grodansparadis/can4vscp_sanfrancisco_barometer/docs/BMP180 Barometric Pressure Sensor Hookup - learn.sparkfun.com_files/52cf0a67ce395f924c8b4569.jpg

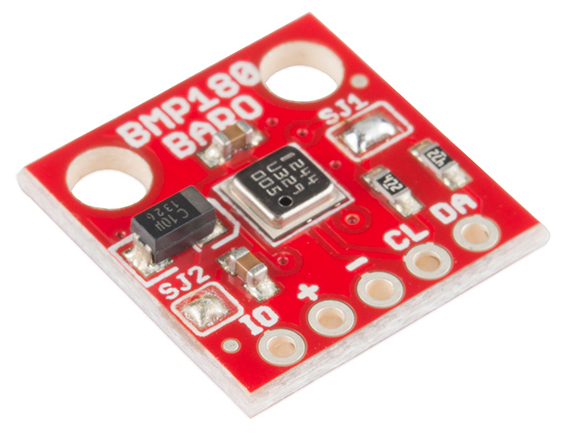
docs/BMP180 Barometric Pressure Sensor Hookup - learn.sparkfun.com_files/52cf0a67ce395f924c8b4569.jpg
