grodansparadis/can4vscp_sanfrancisco_barometer/docs/Oru-Te-EXE084-EL108-04.pdf

Örebro universitet | Örebro University
Institutionen för teknik | Department of technology
701 82 Örebro | SE-701 82 Örebro, Sweden

## Examensarbete 10 po‰ng C-nivÂ

# KONSTRUKTION OCH TILLVERKNING AV

# DENSITETSMƒTARE

## Johan Landmark och Oscar Tryggvesson

## Elektronikingenjˆrsprogrammet 120 po‰ng

## ÷rebro vÂrterminen 2004

Examinator: Sune Bergelin
Handledare: Thorbjˆrn Andersson

Luftdensitetsm‰tare | 2005-05-22

## Fˆrord

Vi vill tacka fˆljande personer. Kjell MÂrdensjˆ fˆr din hj‰lp med programmering av AVR-processorn, Torbjˆrn Andersson (Telnek) fˆr ditt aktiva stˆd genom hela projektet, Thomas
M. Poms fˆr dina idÈer kring konstruktionen av vÂr prototyp, fˆr ert stˆd i vÂrt projektarbete.

÷rebro 2002-12-11

__________________ | __________________
Johan Landmark | Oscar Tryggvesson

## Sammanfattning

Examensarbetet bestÂr av att konstruera en prototyp fˆr m‰tning av luftdensitet i f‰lt. Prototypen ‰mnar underl‰tta inst‰llningarna av fˆrgasare dÂ den ger m‰tv‰rden kontinuerligt pÂ plats. Fˆrhoppningsvis kommer den att spara tid till anv‰ndaren dÂ han/hon inte behˆver sˆka efter v‰rden fˆr att sedan r‰kna ut luftens densitet.

Hj‰rnan i prototypen bestÂr av en AvR mikroprocessor som utfˆr ber‰kningar och visar resultatet pÂ en LCD-display. Densiteten ber‰knas utgÂende frÂn luftfuktighet, lufttryck och temperatur vilket fÂs frÂn givare inbyggda i konstruktionen.

Kraven fˆr examensarbetet ‰r att bygga en prototyp som klarar av att m‰ta luftens densitet i temperatur omrÂdet -10ºC till +50ºC. Fˆr en mer detaljerad beskrivning se kravspecifikationen sid. 9.

MÂlet med vÂrt projekt ‰r att konstruera prototypen inom 10 veckor samt att uppfylla vÂra krav.

Resultatet av projektet med h‰nsyn taget till fˆruts‰ttningar, anser vi blivit bra. Produkten blev aldrig helt f‰rdigkonstruerad och noggrannheten i m‰tningen blev inte heller vad vi hade t‰nkt oss. Trots detta har vi l‰rt oss mycket inom detta nya omrÂde.

## Abstract

Our thesis consists in developing a prototype for field measurement that measures air density. The prototype is meant to relieve the job when calibrating fuel injectors when it provides measurement values continuously. Hopefully it will save time for the user thus he/she doesnít need to look for air density values.

The brain in our construction is the AvR microprocessor that performs calculations and presents the result on an LCD-display. The air density is calculated by values given from the sensors.

The objektive was to build a prototype that manages to calculate the air density between -10°C to +50°C. For more detailed specification se page 9.

Our target was to construct the prototyp within 10 weeks and to satesfy our demands.

The project result considering the limited resources in terms of material, we think that the thesis has worked out well. The product never got finished and the accuracy didnít get as good as we hoped. However we learned a lot in this new area.

## InnehÂllsfˆrteckning

## Bilder

## 1 Introduktion

### 1.1 Bakgrund

Vid karting, gokartt‰vlingar, trimmas motorernas olika delar fˆr att uppnÂ optimal prestanda. En av de viktiga aspekterna ‰r fˆrgasarna eftersom det ‰r de som fˆrser motorn med br‰nsle. N‰r man justerar fˆrgasarna har luftfuktigheten en viss betydelse pÂ hur man st‰ller in dem. DÂ fˆretaget Telnik fÂtt i uppgift att tillverka en smart lˆsning till att m‰ta luftens densitet sÂ att man pÂ plats direkt kan justera fˆrgasarinst‰llningarna har vi Âtagit oss att lˆsa uppgiften som ett examensarbete och tillverka en mobil prototyp fˆr test i f‰lt.

Den stora fˆrdelen med att kunna m‰ta luftens densitet mobilt ‰r att man inte behˆver ta h‰nsyn till var i v‰rlden man t‰vlar dÂ m‰tningen och inst‰llningarna kan gˆras pÂ plats.
En lˆsning till problemet skulle spara tid och pengar, vilket ‰r tvÂ viktiga aspekter.

### 1.2 Projekt beskrivning

Projektets slutgiltiga mÂl ‰r att kunna m‰ta luftens densitet kontinuerligt.Fˆr att Âstadkomma detta kr‰vs fˆljande parametrar:
! Luftfuktighet

! Lufttryck

! Temperatur

PÂ uppdrag av Telnik och med anledningar frÂn vÂr utredning skall en prototyp tillverkas fˆr test i f‰lt. Uppgiften omfattar ‰ven en utredning om hur noggrant densiteten kan m‰tas med de kommersiellt tillg‰ngliga komponenterna med h‰nsyn tagen till vÂr budget.

### 1.3 Fˆruts‰ttningar

Fˆruts‰ttningarna fˆr konstruktionen och tillverkningen av prototypen ‰r att anv‰nda oss av en AvR processor och allt befintligt material pÂ skolan fˆr att pÂ sÂ s‰tt s‰nka kostnaderna.

### 1.4 Kravspecifikation

### 1.4.1 MiljˆtÂlighet

! Prototypen skall kunna anv‰ndas i temperaturomrÂdet -10 till +50 grader celsius.

! Prototypen skall vara dropps‰ker, tÂla l‰ttare duggregn samt mild behandling vid anv‰ndnig.

### 1.4.2 Enhetskrav

! Prototypens mÂtt fÂr ej ˆverskrida mÂtten: 150*150*100mm.

! Prototypen skall kunna redovisa de olika parametrarna pÂ en LCD-display samt vara fˆrsedd med en knappsats fˆr att kunna mata in data.

! Prototypen skall vara fˆrsedd med RS-232 fˆr kommunikation, in/ut, med en station‰r enhet.

! Prototypen skall klara av att m‰ta och lagra data under 24 timmar.

! Batteri fˆr drift i 24 timmar erfordras samt en extern sp‰nningsmatning pÂ 10-36volt.

### 1.4.2 Budget

Komponentpriser i prisklassen 200 sek, avseende temperatur, lufttryck och luftfuktighetsgivare.

## 2 Specifikation

### 2.1 Introduktion

I bˆrjan av vÂrt arbete studerade vi vÂrt problem och fˆrsˆkte komma fram till den billigaste och b‰sta lˆsningen. N‰r vi funderade pÂ vilken lˆsning till problemet som skulle passa b‰st tog vi h‰nsyn till fˆljande aspekter:

! Tidsaspekten, att lˆsa uppgiften inom 10 veckor.

! Kostnadsaspekten, att kunna realisera vÂrt mÂl med hˆgsta kvalitet men ‰ndÂ hÂlla nere kostnaderna.

! Funktionalitetsaspekten, att konstruera ett system som ‰r stabilt och med komponenter som dÂ kan ge stabila och exakta v‰rden.

! Materielaspekten, tillgÂng till befintligt och anv‰ndbar materiel pÂ skolan, hÂrdvara samt mjukvara.

N‰r vi utredde vilken lˆsning som skulle passa oss kom vi fram till att vi skulle anv‰nda oss av en mikroprocessor fˆr att utfˆra ber‰kningen av luftdensiteten. Vi skulle tillverka ett eller flera kretskort som passade vÂra komponenter och det skal som vi skulle anv‰nda oss av.

### 2.2 Huvudsyfte

HuvudidÈn med projektet ‰r att tillverka en smidig mobil m‰tstation som drivs av kommersiella batterier. Den blir ett enkelt m‰tinstrument, multimeter, som enkelt kan packas ned och fˆrflyttas utan problem. V‰l pÂ plats skall anv‰ndaren snabbt kunna m‰ta luftens densitet med nÂgra enkla knapptryckningar. Anv‰ndaren skall inte behˆva oroa sig fˆr att prototypen kommer till skada vid anv‰ndning dÂ den ‰r skyddad mot fukt, damm och tÂl mild behandling.
Vid anv‰ndning av prototypen anv‰nds en enkel knappsats fˆr olika val av m‰tning samt meny val av vad som skall visas pÂ displayen.

### 2.3 Anv‰nd mjukvara

### 2.3.1 Scintilla Text Editor

Till en bˆrjan var Scintilla ett enkelt dokumentationsprogram som sedan utvecklades till ett smidigt program d‰r man kan bygga, kompilera och programmera sin hÂrdvara. Scintilla klarar av mÂnga av dagens anv‰nda programmeringssprÂk som:
C.C++ och Assembler.

### 2.3.2 Multisim

Kretsschemat ‰r byggt med hj‰lp av programmet Multisim. Multisim ‰r ett simuleringsprogram fˆr elektronik, d‰r man kan simulera bÂde analoga och digitala kopplingar samt en mix av dessa. Med programmet kan man ‰ven exportera (transformera) kretsschema till programmet UltiBoard d‰r man kan konstruera kretskort. Med programmet Multisim kan anv‰ndaren bygga upp sin koppling pÂ sk‰rmen och testa dess funktion.

## 3 Teori

### 3.1 Sensorer

Fˆr att klara av att m‰ta luftdensiteten pÂ ett bra s‰tt kr‰vs att man anv‰nder sensorer som med god noggrannhet m‰ter sitt specifika omrÂde.

N‰r vi valde sensorer, givare, grundade vi vÂra beslut enligt fˆljande.
! Ett bra pris, som gˆr att de hamnar inom vÂr budget.
! Bra linjaritet, fˆr b‰ttre m‰tnoggrannhet.
! De ska klara av kravspecifikationen.
! Vi undersˆkte liknande konstruktioner fˆr att se, vilka sensorer som anv‰nts vid liknande projekt.

### 3.1.1 Temperatursensor (SMT160)

Temperatursensorn Smarttemp frÂn Smartec har fˆljande egenskaper:

! Kr‰ver endast en ledig digitalport pÂ din mikroprocessor.
! Inbyggd A/D omvandlare med pulsbreddsmodulerad frekvensutgÂng vilket ger enkel interface mot omv‰rlden.
! Linj‰r utgÂng.
! Onoggrannheten i intervallet -30 till +100ºC ‰r ± 0.5ºC.
! Matningssp‰nning: +4.7 till +7.0 Volt.
! Strˆmfˆrbrukning: <200uA.

Figur 3.1.1 Temperatursensor (SMT160)

Vid m‰tning av temperaturen ansluts utsignalen frÂn sensorn till en digital port pÂ mikroprocessorn. Sensorn avger en pulsmodulerad signal som vi med processorn samplar signalen, i vÂrt fall 40000ggr, till en îdutycycleî, som sedan matematiskt gˆrs om till temperatur enligt specifikationen frÂn sensorns datablad. Funktionen som anv‰nds heter îdigital_samplingî och finns som bilaga tillsammans med resterande c-kod.

### 3.1.2 Trycksensor (mpx5100ap)

Trycksensorn mpx5100 frÂn Motorola har fˆljande egenskaper:

! M‰ter tryckskillnad ˆver 15 till 115kPa.
! M‰tfel: ±2,5% mellan 0 till 80°C.
! Kr‰ver endast en ledig analogport pÂ din mikroprocessor. ! Analog utsignal mellan 0.2 till 4.7Volt (0 till 100%RH). ! Inbyggt referenstryck.
! Matningssp‰nning: +4.75 till +5.25Volt

Figur 3.1.2 Trycksensor (mpx5100ap)

Vid m‰tning med trycksensor ‰ndv‰nds en analog ingÂng pÂ mikroprocessorn som omvandlar liksp‰nningar mellan 0 och 5 volt till ett heltal mellan 0 och 1023. Med andra ord ‰r upplˆsningen 5/1023=4.88758mv. Komponenten ‰r v‰ldigt k‰nslig g‰llande matningssp‰nning (se bild nedan) sÂ d‰rfˆr har vi kompletterat just denna koppling med en mer exakt matningssp‰nnig se avsnittet îkretskopplingarî.

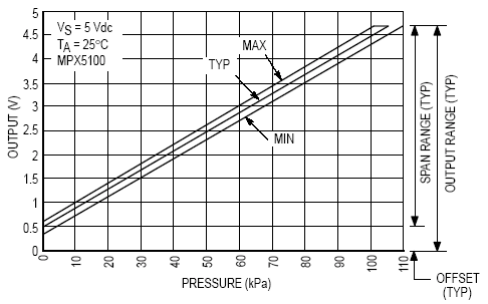
[picture p11: figure]

Figur 3.1.2 Matningssp‰nningsk‰nslighet

### 3.1.3 Fuktsensor (SMTHS10)

Fuktsensorn SMTHS10 frÂn Fabr Smartec har fˆljande egenskaper:
! En kapacitiv fuktsensor som klarar 100 % luftfuktighet utan att ta skada. ! Sensorn har en linj‰r skala frÂn 0 till 100 %
! Sp‰nning: 5V ~max
! FrekvensomrÂde pÂ 10 till 100 kHz
! FuktomrÂde mellan 0 och 100% RH
! Kapacitans (60%) pÂ 240pF ±20%
! KapacitansomrÂde mellan 40pF ±12% (0 till 100% RH) ! Linjaritet runt ±2% RH
! LÂngtidsstabilitet runt ±3%RH (12mÂn)
! Reaktionstid pÂ 60 sek
! TemperaturomrÂde mellan -40 till +120ºC

Figur 3.1.3 Fuktsensor (SMTHS10)
Funktion:
En icke-ledande tunn folie fˆrses med ett tunt guldskikt pÂ vardera sida. Denna tunna folie utgˆr ett dielektrikum och guldskiktet utgˆr plattorna i en kondensator. Den isolerande folien fungerar som en îsvampî och absorberar fukt. Detta leder till att îkondensatornsî kapacitans ‰ndras i fˆrhÂllande till fukten i folieskiktet.
Fˆr att kunna m‰ta kapacitansfˆr‰ndringen anv‰nds timerkretsar fˆr att fÂ ett referensmÂtt d‰r pulsens bredd fˆr‰ndras beroende pÂ kapacitansen i fuktsensorn. Pulsens bredd m‰ts med hj‰lp av en timer i AvR- kretsen.

Timerfunktionen triggas dÂ den k‰nner av en positiv flank och en tid sparas i ett minne, samma sak h‰nder vid den negativa flanken och en tidsskillnad uppstÂr. PÂ sÂ vis fÂs pulsens bredd med hˆg noggrannhet eftersom processorn arbetar med 8 MHz leder detta till att vi kan m‰ta pulsens tid ,l‰ngd, med en noggrannhet pÂ 125ns. http://www.tfe.umu.se/courses/elektro/elmat1/AA_DAT2002v36/Seminar%20El_Ding_2003/Gr %20(4)/Gr4_A/fuktgivare%20grupp4.doc http://www.cyfronika.com.pl/ARCHIWUM/smths10.pdf

us

V

Positiv flank | Negativ flank

3.2 ÷vriga komponenter
Fˆr att kunna anv‰nda sensorerna kr‰vdes fˆljande komponenter som ett komplement fˆr att fÂ ˆnskade utsignaler frÂn dem samt mikrokontroller fˆr att styra systemet.

### 3.2.1 Sp‰nningsregulator 78L05

Sp‰nningsregulatorn anv‰nds fr‰mst fˆr att trycksensorn ‰ndrar sin utsignal betydligt om matningssp‰nningen ‰ndras. Fˆr att minska felm‰tningar anv‰nds denna sp‰nningsregulator. Den har fˆljande egenskaper:
! 6mA strˆmfˆrbrukning (max)
! Temperatur omrÂde ñ30ºC - 130ºC
! Matningssp‰nning +4,7V - +7,0V ! Utsp‰nningstolerans ±5%
! Sp‰nningsfall: 1.7 Volt typ

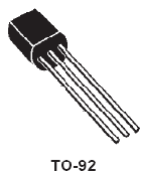
[picture p12: figure]

Figur 3.2.1 Sp‰nningsregulator 78L05

### 3.2.2 AtmelMega16L

Mikrokontrollern frÂn Atmel ‰r m‰tsystems hj‰rna. Det ‰r den som programmeras att utfˆra ber‰kningar och utfˆra A/D omvandling. H‰r ‰r nÂgra av mikrokontrollerns egenskaper:
! 16Kbyte programmerbar FLASH minne.
! 512byte EEPROM.
! 8MHz klockfrekvens.
! 32 st. programmerbara I/O pinnar.
! A/D omvandlare

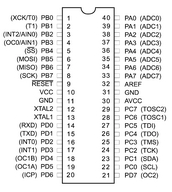
[picture p13: figure]

Figur 3.2.2 Atmega16L

OvanstÂende egenskaper ‰r bara en liten brÂkdel av vad som finns att h‰mta. Fˆr alla detaljer kring mikrokontrollern h‰nvisar vi till databladet:
http://www.elfa.se/pdf/73/736/07367246.pdf

### 3.2.3 Timerkrets NE555

Vid uppbyggnaden av konstruktionen anv‰nde vi oss av timerkretsar frÂn NEC NE555. Timerkretsen har fˆljande egenskaper:
! Temperaturstabilitet 0.0005%/ ºC.
! Justerbar arbetscykel (dutycycle).
! Arbetsfrekvens stˆrre ‰n 500KHz. ! Pulsrepetition frÂn 1us till 1h.
! Pulsbredsmodulation.
! Tid fˆrdrˆjnings generering.

Figur 3.2.3 Timerkrets NE555

Eftersom man inte kan m‰ta kapacitansfˆr‰ndringar med mikrokontrollern anv‰nde dessa timerkretsar dÂ pulsens bredd ‰ndras i samband med kapacitansfˆr‰ndringar. Efter det att en fyrkantspuls erhÂllits kan m‰tningar pÂ denna utfˆras och konverteras, med ber‰kningar i processorn, till ett flyt tal och presenteras pÂ LCD-displayen.

### 3.3 Formler

Vid ber‰kning av densitet ‰r det den ideella gaslagen som g‰ller i grund och botten:

### 3.3.1 Den ideella gaslagen

P*V = n*R*T

P= Tryck
V= Volym
n= Antalet molekyler
R= Gaskonstant
T= Temperatur

### 3.3.2 Densitets formeln

Densitet ‰r helt enkelt antalet molekyler pÂ en viss volym och beskrivs enligt nedan:

D = n / V

D = Densitet
n = Antalet molekyler
V = volym

Eftersom luftfuktigheten spelar sin roll i m‰tandet av densitet mÂste trycket ber‰knas fˆr torr respektive fuktig luft. NedanstÂende ekvation realiserar detta:

D = densitet, kg/m³
Pd = Trycket fˆr torr luft, Pascal
Pv= Trycket fˆr fuktig luft, Pascal
Rd = Gas konstanten fˆr torr luft, J/(kg*degK) = 287.05
Rv = Gas konstanten fˆr fuktig luft (vaporised), J/(kg*degK) = 461.495
T = Temperatur, degK = deg C + 273.15

UtifrÂn ovanstÂende formel ber‰knas densiteten. En bra sida som beskriver mer detaljrikt ‰r fˆljande: http://wahiduddin.net/calc/density_altitude.htm

### 3.4 Bilder

### 3.4.1 Kopplingsplatta

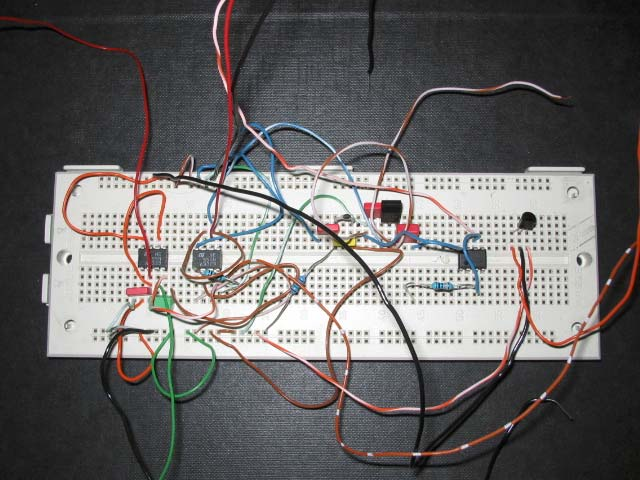
[picture p14: figure]

Ovan ges exempel pÂ hur det kunde se ut dÂ vi testa olika kretskopplingar fˆr att fÂ ut sÂ bra noggrannhet ur sensorerna som mˆjligt.

### 3.4.2 AvR-kort

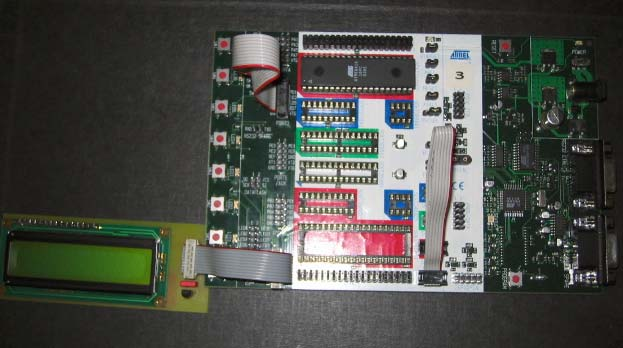
[picture p15: figure]

H‰r ser ni AvR-kortet som vi anv‰nde oss av vid programmering av processorn och display fˆr visning av m‰tv‰rden frÂn sensorerna.

### 3.5 Kretslˆsningar

Fˆr att fˆrenkla projektet delades vissa omrÂden in i olika delar, d‰rav olika kretsar som realiserar ett visst omrÂde.

### 3.5.1 Luftfuktighetskretsen

NedanstÂende kretsschema realiserar en komplett luftfuktighetsgivare med alla dess komponenter. Komponenten C2 i vÂrt kretsschema realiserar fuktighetssensorn, SMTHS 10, dÂ den avger en kapacitans. Kopplingen som tillverkades i multisim gav oss mˆjligheten att ‰ndra v‰rden pÂ komponenterna fˆr att fÂ ett sÂ bra resultat som mˆjligt n‰r den skulle kopplas upp

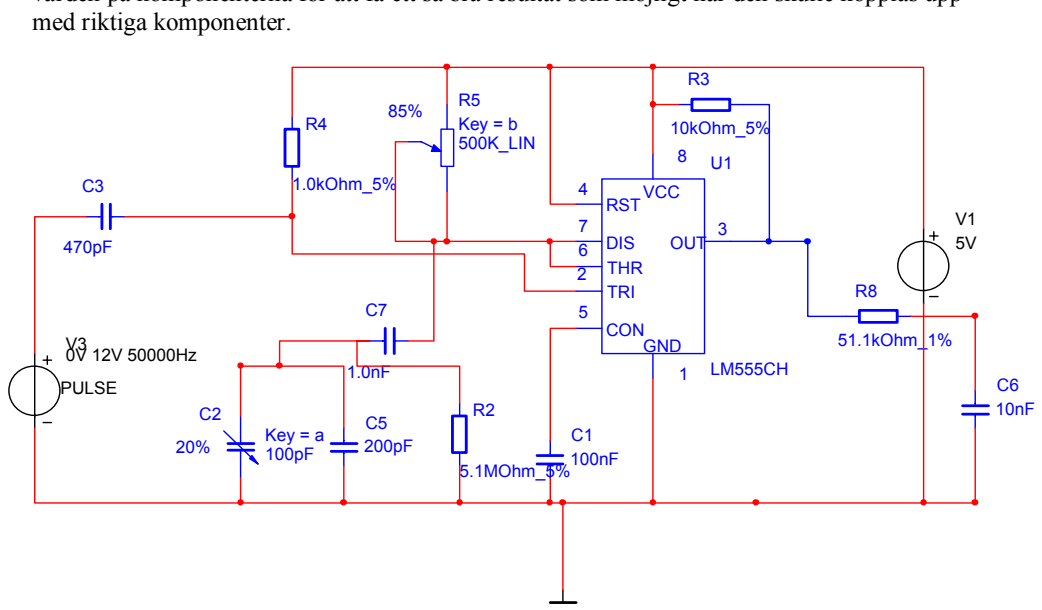
[picture p16: figure]
med riktiga komponenter.; DIS; OUT; RST; THR; CON; TRI; GND; VCC; PULSE; 10kOhm_5%; 5.1MOhm_5%; 1.0kOhm_5%; Key = a 100pF 20%; Key = b; 500K_LIN; 51.1kOhm_1%

### 3.5.2 Lufttryckskretsen (sp‰nningsmatning)

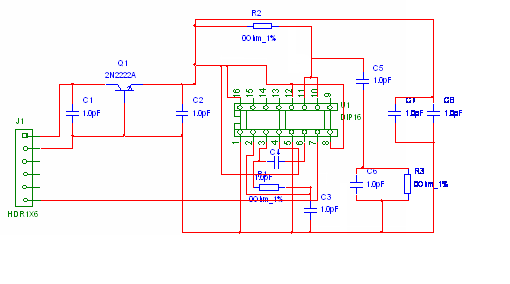
[picture p17: figure]

VÂr trycksensor var som tidigare n‰mnt v‰ldigt k‰nslig n‰r det g‰llde matningssp‰nning. Vi tillverkade dÂ en krets fˆr att stabilisera matningssp‰nningen sÂ att m‰tv‰rdena skulle stabiliseras och felmarginalen minska. Nedan ses ett fˆrslag till hur kretslˆsningen ser ut.

### 3.6 Noggrannhet

En undersˆkning kring noggrannheten vid m‰tning av luftens densitet till‰mpades fˆr att kunna se hur noggrant m‰tningen kunde utfˆras. Vid ber‰kningen av det totala felv‰rdet anv‰ndes formler frÂn avsnittet formler (kap 3.3).

### 3.6.1 Maximalt felv‰rde

DÂ formeln fˆr luftens densitet ser ut enligt fˆljande:

Man kan konstatera att ett max-fel uppstÂr n‰r temperaturens och fuktens v‰rde ‰r sÂ litet som mˆjligt, samtidigt som trycket ‰r stort.
Min-fel uppstÂr dÂ temperaturgivaren och fuktighetsgivaren ger ifrÂn sig stora v‰rden, samtidigt som trycksensorn indikerar ett fˆr litet v‰rde.

Vi antar att fˆljande v‰rden st‰mmer:
Tryck: 100kPa
Fukt:40% RH
Temperatur:20 ºC

## 4 Genomfˆrande

### 4.1 ArbetsgÂng

Vi bˆrjade vÂrt arbete med att ta reda pÂ vad luftdensitet egentligen ‰r och vilka faktorer som spelar in. N‰r vi sedan fÂtt klart fˆr oss att vi behˆvde temperatur, lufttryck och luftfuktighet fˆr att kunna r‰kna ut luftdensiteten, best‰mde vi oss inom kort fˆr att koppla dessa givare samman i en AVR-processor.

I uppgiften ingick ‰ven att ta reda pÂ hur stor noggrannhet vi kunde fÂ pÂ vÂr luftdensitetsm‰tare inom den budgeten vi var begr‰nsade till. Fˆr att ta reda pÂ detta sˆkte vi pÂ Internet fˆr att hitta b‰ttre sensorer ‰n de som skolan hade att erbjuda. Vi fann en fuktsensor, HS1101, som hade mycket hˆg noggrannhet och mycket litet avvikande fel. Denna var vi dock tvungna att best‰lla frÂn Tyskland och leveranstiden var pÂ ˆver tvÂ veckor, dessutom hade den en aning fˆr hˆgt pris fˆr vad vÂr budget klarade av. Vi hittade ‰ven en passande trycksensor, SM565. DÂ vi ist‰llet fick trycksensorn mpx5100ap frÂn skolan som vi dÂ trodde var b‰ttre¹
anv‰nde vi oss av
den. Vi funderade ‰ven pÂ att bygga ihop fuktgivaren med kretsen DS1616 som hade en inbyggd temperatursensor, men eftersom detta bÂde skulle bli krÂngligare och ˆverflˆdigt avvisade vi ‰ven detta fˆrslag.

Det slutgiltiga fˆrslaget bestod nu av tre separata sensorer. En temperatursensor med bra noggrannhet och som dessutom ‰r billig, en trycksensor med ett inre referenstryck och en fuktsensor med mycket goda egenskaper.

N‰r vi fÂtt vÂr AVR-rack provade vi fˆrst med nÂgra enklare program fˆr att fˆrsˆka hitta in- och utgÂngar pÂ processorns portar och att samtidigt l‰ra oss mer om AVR-processorn. VÂrt n‰sta mÂl var att implementera funktioner fˆr att anv‰nda oss av temperatursensorn som vi skulle anv‰nda oss av. Temperatursensorn SMTHS10 fick vi att fungera relativt snabbt dÂ det fanns f‰rdiga funktioner och klasser att anv‰nda.
N‰r vi k‰nde att kunskapen om vÂr AVR ñkrets var tillr‰ckliga pÂbˆrjade vi att implementera funktioner fˆr resterande sensorer och uppbyggnaden av ett program som kunde avl‰sa de olika sensorerna och ta fram luftdensiteten. Allt eftersom arbetet med prototypen fortlˆpte utvecklades mjukvaran fˆr att tillfredsst‰lla vÂr hÂrdvarukonfigurationen. Arbetet med att fÂ fram hˆgsta mˆjliga noggrannhet blev mycket tidskr‰vande dÂ vi var tvungna att komma pÂ egna s‰tt att anv‰nda sensorerna pÂ. Vi studerade mÂnga kretslˆsningar fˆr att fÂ fram sÂ mycket som mˆjligt frÂn vÂra sensorer. N‰r vi hittat en l‰mplig kretslˆsning Âterstod programmeringen till processorn fˆr att fÂ fram ˆnskv‰rd data²
. Vi gjorde ‰ven en kalibrering av sensorerna fˆr temperatur och fˆr fuktighet. Fˆr att kalibrera trycksensorn behˆvdes avancerad utrustning som vÂr budget inte klarade av. Fˆr att testa temperatursensorn anv‰nde vi oss av en digital termometer som m‰tte temperatur med tillr‰ckligt god noggrannhet. Fˆr fuktsensorn anv‰nde vi oss av kemikalier fˆr att skapa inkapslade miljˆer med en exakt luftdensitet.
N‰r detta var avklarat pÂbˆrjade vi utveckling av vÂrt program fˆr att fÂ det drifts‰kert och l‰tt att utveckla vid behov.

### 4.2 Programuppbyggnad

Huvudprogrammet heter Maektuub V1.0 och ‰r uppbyggt med objektorienterad programmering i Scintilla Text Editor (C++). Programmet fungerar som en tillstÂndsmaskin d‰r anv‰ndaren v‰ljer vilken information som skall visas pÂ LCD-displayen genom knapptryckning pÂ AVR-kretsen. Fˆljande tillstÂnd finns i vÂrt program:

! Temperaturm‰tning

! Tryckm‰tning

! Luftfuktighetsm‰tning

! Densitet

1
Detta m‰rktes senare att det inte riktigt st‰mde.
2
Mer om detta i Programuppbyggnad 4.2.

### 4.2.1 Maektuub V1.0 Main.c

Nedan kommer vi att gÂ igenom programmet del fˆr del med programmeringskod och fˆrklaringar. Main.c fungerar som en o‰ndlig loop som endast ‰ndrar tillstÂnd dÂ anv‰ndaren kr‰ver det genom att trycka pÂ en knapp. Nedan visar vi kort hur sj‰lva programmet ‰r uppbyggt i c-kod.

Interupt
{
input capture
};

While(1)
{
CASE 1
{
sensor_smt160_read(&theSensor,40000,type); | //TEMPERATUR
lcd4
}
CASE 2
{
sensor_mpx5100_read(&theSensor1); | //LUFTTRYCK
lcd4
}
CASE 3
{
signal(sig_input_capture1) + smths10 | //LUFTFUKTIGHET
lcd4
}
CASE 4
{
sensor_smt160_read(&theSensor,40000,type); | //BERƒKNING
sensor_mpx5100_read(&theSensor1); | AV LUFTDENSITET
signal(sig_input_capture1) + smths10
airdens_calc
lcd4
}
};
I stort kan vi genom den enkla kodbeskrivningen fˆrklara programmets uppbyggnad.
DÂ vi startar vÂrt program sker, som vanligt, initiering av funktioner, variabler, objekt och konstanter. Programmet ‰r det kodat sÂ att vi hamnar i den fˆrsta case satsen, CASE 1, av fyra st.

### 4.2.2 CASE 1 Temperaturm‰tning

I denna sats m‰ter vi temperaturen med vÂr temperatursensor smt160 genom att ropa pÂ funktionen sensor_smt160_read. Fˆr att fÂ en stˆrre ˆversikt vad som h‰nder n‰r funktionen kˆrs visar vi nedan delar av k‰llkoden fˆr denna funktion.

float sensor_smt160_read(sensor_smt160 *this,double n,char type)
{
this->type=type;
this->n=n;
this->duty_cycle=digital_sampling(this->port,this->bit_mask,this->n); this->temp= (float) this->duty_cycle/(float)this->n; this->temp=(((this->temp-0.32)/0.0047));
return this->temp;
}

Som vi tidigare n‰mnt ger denna sensor en pulsbreddsmodulerad signal pÂ utgÂngen. I funktionen ser vi att îduty_cycleî fÂr v‰rdet av îdigital_samplingî som ‰r pulsbreddsmoduleringen. N‰r vi fÂtt sensorns îduty_cycleî, omvandlar vi den med formler frÂn sensorspecifikationen fˆr att fÂ ett flyttal som presenterar temperaturen. Detta flyttal ‰r det som returneras frÂn funktionen. Ist‰llet fˆr att skriva 30 rader kod kan vi nu fˆrenklat skriva en rad i main , sensor_smt160_read(&theSensor,40000,type);, och pÂ sÂ vis fÂ ett snyggare och mer strukturerat program.

### 4.2.3 CASE 2 Lufttrycksm‰tning

Ungef‰r samma tillv‰gagÂngss‰tt h‰r som i fˆregÂende case sats. Vi ropar pÂ funktionen sensor_mpx5100 och fˆljande kod kˆrs.

io_ai ai1;
float sensor_mpx5100_read(sensor_mpx5100 *this)
{
this->heltal=io_ai_read(&ai1); this->Pa=(this->heltal*0.00488758)/0.04086956;
return this->Pa;
}

Denna sensor returnerar en analog signal mellan 0,2V-4,7V beroende pÂ trycket , 15-115kPa . Fˆr att kunna omvandla den signalen till ett flyttal som vi kan anv‰nda i vÂra ber‰kningar anv‰nder vi oss av en analog ingÂng med 10 bitars upplˆsning. Efter att insignalens magnitud avl‰sts pÂ den analoga ingÂngen till processorn ber‰knar vi exakta antalet kPa som denna insignal motsvarar och returnerar v‰rdet till main funktionen.

### 4.2.3 CASE 3 Luftfuktighetsm‰tning

I detta tillstÂnd m‰ter vi luftfuktigheten. DÂ vÂr konstruktion med luftfuktighetsm‰taren ger en variabel pulsbredd pÂ utgÂngen som ‰r ytterst liten, kom vi fram till att om vi ville ha den b‰sta noggrannheten var vi tvungna att anv‰nda oss av processorns îinput capture unitî. En trigger i processorn som k‰nner av positiv respektive negativ flank pÂ en puls. Genom att m‰ta tiden mellan positiv och negativ flank med klockfrekvensen 16MHz i processorn skulle vi komma sÂ n‰ra mÂlet som mˆjligt. Fˆr att anv‰nda îinput capture unitî var vi tvungna att anv‰nda oss av specifika kommandon och bygga en avbrottsrutin, som vi kommer att fÂ se nedan.

asm(" SEI ");

Detta kommande betyder att globala avbrott tillÂts och processorn hoppar nu till avbrottsrutinen dÂ den k‰nner en positiv flank pÂ ICP, Input Capture Pin. I avbrottsrutinen nedan m‰ter vi sedan tiden mellan positiv flank och negativ genom att l‰sa av ICR1, Input Capture Register, och tilldelar en variabel v‰rdet innan vi byter flank och l‰ser av den negativa flankens tidsv‰rde. Fˆr att Âstadkomma tidsm‰tningen kr‰ver programmeringen att en hel del register tilldelas v‰rden. Fˆr att visa detta pÂ ett enkelt s‰tt ÂskÂdliggˆr vi programmkoden fˆr avbrottsrutinen nedan och kommenterar den.

SIGNAL(SIG_INPUT_CAPTURE1)
{
if ( bTCCR1B.ices1 )
{
hi=ICR1
bTCCR1B.ices1 = 0;
}
else
{
lo=ICR1;
bTCCR1B.ices1 = 1;
bTIMSK.ticie1 = 0;
}

Ovan ser vi en if/else sats, vi bˆrjar med if delen. Om bTCCR1B.ices1 har v‰rdet î1î k‰nner ICP, input capture pin, av positiva flanker och om den har v‰rdet î0î negativa. Vi antar att den har v‰rdet î1î. Nu kommer variabeln hi att tilldelas tidsv‰rdet som sparas i ICR-registret. Efter detta byter vi nu till avl‰sning av den negativa flanken genom att tilldela TCCR1B-registret v‰rdet î0î, bTCCR1B.ices1 = 0;. Den negativa flankens tidsv‰rde kommer nu att sparas i ICR1 registret och vi har vÂr tidsskillnad.
Vi ger TIMSK.ticie1 v‰rdet 0, vilket resulterar i att avbrott inte l‰ngre tillÂts. Med nÂgra enkla else/if satser r‰knar vi sedan ut tidsskillnaden och dÂ vi vet pulsens bredd m‰tt i tid kan vi r‰kna ut motsvarande luftfuktighet.

### 4.2.4 CASE 4 Luftdensitetsber‰kning

I detta tillstÂnd anv‰nder vi oss av alla ovanstÂende funktioner fˆr att fÂ v‰rden pÂ temperatur, lufttryck och luftfuktighet fˆr att kunna utfˆra luftdensitetsber‰kningen. Det enda som ‰r nytt fˆr detta tillstÂnd ‰r ber‰kningsdelen. Fˆr denna ber‰kning h‰nvisar vi till avsnittet îFORMLERî.

### 4.3 Flˆdesscheman

NedanstÂende flˆdesscheman ger en grafisk inblick i hur de olika programmeringsmodulerna ‰r uppbyggda.

### 4.3.1 Maektuub V1.0 (main.c)

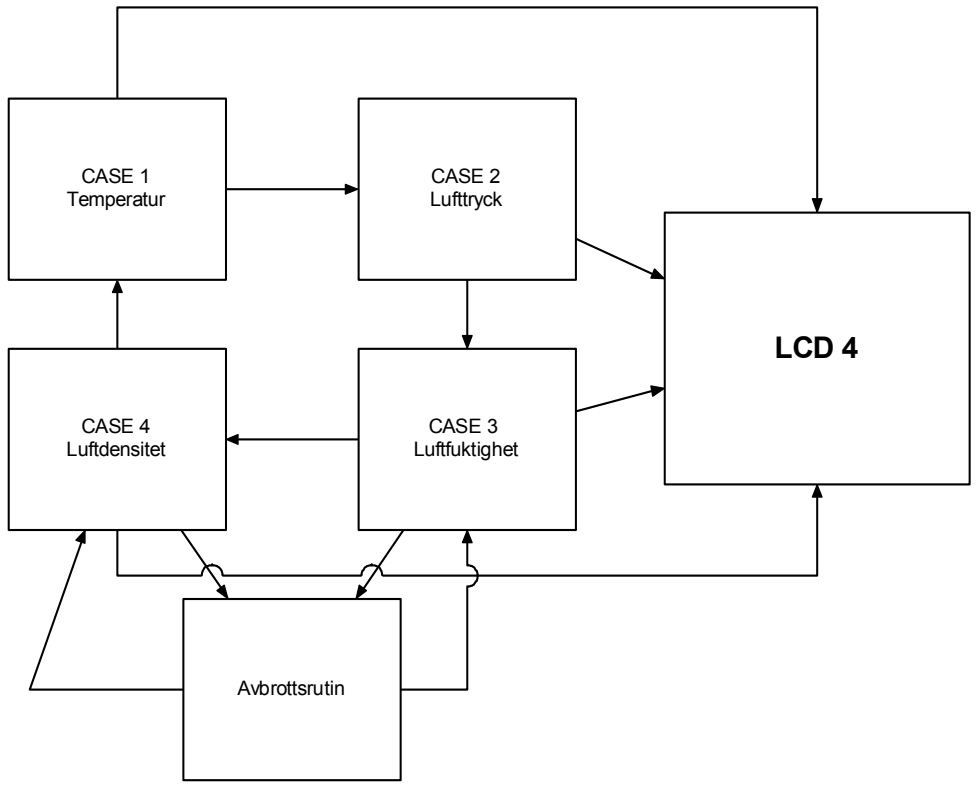
[picture p18: figure]
CASE 4 Luftdensitet; CASE 2 Lufttryck; CASE 3 Luftfuktighet; Avbrottsrutin; LCD 4; CASE 1 Temperatur

### 4.3.2 CASE 1 Temperatur Sensor_smt160.c

Digital sampling

Ber‰knningar | Main

### 4.3.3 CASE 2 Sensor_mpx5100.c

Io_ai read

Ber‰knningar | Main

### 4.3.4 CASE 3 Sensor_smths10.c

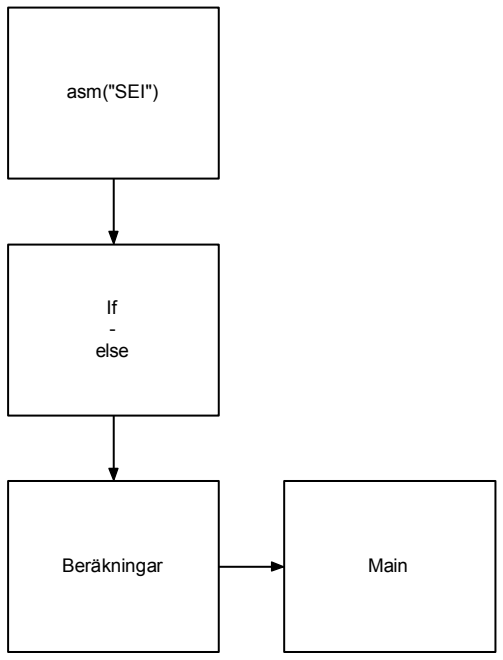
[picture p19: figure]
asm("SEI"); If - else; Ber‰kningar; Main

### 4.3.5 CASE 4 Luftdensitet

CASE 1

CASE 2

CASE3

Ber‰kningar | Main

## 5.1 Resultat

### 5.1 Resultat frÂn m‰tinstrumentet

FrÂn prototypen fÂr vi ut temperatur med noggrannheten < ± 0.5ºC, fukt med noggrannheten ±0,13% samt lufttryck med en noggrannhet pÂ 2,6kPa. Det totala felet fˆr ber‰kningen fˆr luftdensiteten blir dÂ ±0,0666kg/m^3

Menyn ‰r enkel att anv‰nda sig av och v‰rdena kan avl‰sas kontinuerligt.
DÂ detta fortfarande ‰r en prototyp sÂ uppfyller den ‰n inte alla de krav som var satta frÂn bˆrjan.
Prototypen klarar inte det krav fˆr utomhusbruk dÂ den inte fÂtt nÂgon inkapsling. Prototypen har mˆjlighet att kˆras pÂ batterier men fˆr att m‰tinstrumentet ska komma till sin fulla r‰tt kr‰vs det att den blir inkapslad och portabel.

### 5.2 Kalibrering

Vid kalibrering finns det olika tillv‰gagÂngss‰tt. Vi valde metod utgÂende frÂn vÂr budget. En bra och mycket noggrann metod ‰r att installera sensorn i en klimatanl‰ggning som hÂller exakt temperatur, luftfuktighet och lufttryck fˆr att kalibrera sensorn. Detta ‰r dock en dyr variant. Vi anv‰nde oss ist‰llet av olika saltlˆsningar fˆr att kalibrera fuktsensorn. Eftersom vÂr prototyp ‰r kopplat mha. kopplingsplatta sÂ fˆr‰ndrades kapacitansen pÂ fukthetgivaren frÂn dag till dag dÂ vi testade kopplingen. Detta beror pÂ krypkapacitanser i anslutande koppling. Vid kalibrering av temperatursensorn anv‰nde vi oss av en noggrann termometer fˆr att en bra kalibrering och ett litet motstÂnd som vi tillsatte sp‰nning fˆr att alstra v‰rme. Fˆr kalibrering av tryck ÂterstÂr dock problemet med att hitta en billig och relativ enkel metod

Fuktsensorn smths10
Det ‰r sen tidigare k‰nt att om fuktsensorn inkapslas ovanfˆr en lˆsning av Magnesium Nitrat vid temperaturen 20 grader Celsius erhÂlles luftfuktigheten 55% RH. Vid anv‰ndande av Lithium Klorid vid samma temperatur erhÂlles 12% RH. Vid anv‰ndande av Natrium klorid erhÂlles 75.5 % RH. OvanstÂende metod ‰r endast beroende av temperaturen.

Tempsensor smt160
Temperatursensorn vet vi sen tidigare har en noggrannhet i intervallet -30 till +100ºC pÂ ± 0.5ºC. Detta testade vi genom att anv‰nda oss av en noggrann digital termometer kopplad till samma motstÂnd som den sensor vi anv‰nde oss av.

### 5.3 Slutsatts

Som vi m‰rker ‰r det lufttrycksensorn som drar ner noggrannheten. Anledningen till detta beror pÂ att det totala felet frÂn sensorn ‰r hela ±2,5% av Fullscale (0,2 ñ 4,7V). Detta betyder att felet pÂ bara tryckgivaren blir upp till hela ±2,6 kPa. Det totala felet fˆr utr‰kningen fˆr luftdensiteten beror d‰rfˆr till stor del av lufttrycksensorns hˆga felprocent.

Att anv‰nda sig av AVR-processorn var betydligt svÂrare och mer tidskr‰vande ‰n vi fˆrst trodde. Att finna bra funktioner och smarta formler fˆr att anv‰nda oss av de sensorer vi valt att anv‰nda oss av visade sig vara den tyngsta delen av detta arbete. Det svÂra var att finna bra lˆsningar till hur man pÂ ett bra och noggrant s‰tt ˆverfˆr data frÂn sensorerna till processorn. Flera problem har vi stˆtt pÂ som tex. hur mÂnga volt som processorn kan k‰nna av, hur ofta processorn kan k‰nna av en signal, storleken och noggrannhet pÂ insignaler i form av byte, tid mellan positiv flank till en negativ osv.

### 5.1 Diskussion

Varfˆr fick vi inte f‰rdig vÂr prototyp med de krav som var st‰llda frÂn bˆrjan? Finns det saker vi kunde ha gjort b‰ttre fˆr att fÂtt b‰ttre fˆruts‰ttningar att bli klara med prototypen? Vi finner att b‰ttre undersˆkning borde ha gjorts innan vi best‰mde oss fˆr att anv‰nda den trycksensor vi valde. Sp‰nningsmatningen till sensorn var tvungen att vara exakt stabil. Om sp‰nningen ‰ndrade sig, om bara minimalt, ‰ndrade sig utsignalen frÂn den rej‰lt. Sp‰nningsstabilisatorn lˆste problemet och vi kunde sedan forts‰tta arbetet med de andra sensorerna.
I efterhand kan vi konstatera att programmeringen och forskningen runt AVR-processorn blev en alldeles fˆr stor och tidskr‰vande del. Att finna en lˆsning d‰r noggrannheten pÂ densitetsm‰taren st‰lldes pÂ fokus blev ett allt fˆr stort jobb. Ett alternativ skulle ha varit att densitetsm‰taren byggts med enklare komponenter och att i efterhand undersˆkt om nÂgra justeringar till fˆrb‰ttring kunnat ha gjorts. Att bara kasta sig ˆver AVR-processorn var kanske ett annat fel vi gjorde. Kanske fanns det andra processorer vi kunnat ha anv‰nt oss av? Problemet och mÂls‰ttningen fˆr oss blev att hitta den b‰sta lˆsningen fˆr att fÂ sÂ lÂga felprocent frÂn sensorerna. Vi hade sparat mycket tid om vi bara hade valt den enklaste metoden fˆr att lˆsa uppgiften. Men det gjorde vi inte. Men tack vare det har vi fÂtt en djup inblick i hur det ‰r att arbeta med sensorer. En sensor ska ge oss svar pÂ det vi sˆker efter, vare sig det ‰r ljus, tryck, vibrationer eller fukt. Att kunna Âterspegla verkligheten med hj‰lp av sensorer ‰r mycket svÂrt. Det sensorerna ger ifrÂn sig ‰r sp‰nningsfˆr‰ndringar eller kanske pulsfˆr‰ndringar beroende pÂ ur man vill behandla dem. Att finna den b‰sta lˆsningen ‰r mycket svÂr om inte omˆjlig. Men dÂ vi hade en budget att hÂlla oss till sÂ blev den sÂ klart begr‰nsad. Trots detta sÂ fanns det otaliga metoder att anv‰nda sig av dÂ det g‰llde AVR-processorn.

### 5.2 Fˆrb‰ttringar

En fˆrb‰ttring till problemet med m‰tnoggrannheten ‰r att anv‰nda sig av b‰ttre sensorer helt enkelt. Men dÂ till en stˆrre kostnad. Det finns ‰ven b‰ttre processorer med hˆgre upplˆsning pÂ portarna som skulle leda till b‰ttre m‰tnoggrannhet.

Att lˆda fast alla komponenter pÂ ett kretskort och stabilisera alla sensorer frÂn stˆtar som fˆr‰ndrar dess egenskaper skulle ˆka tillfˆrlitligheten avsev‰rt. Att anv‰nda kortare och avsk‰rmade ledare till och frÂn sensorerna skulle ytterligare ˆka tillfˆrlitligheten. Alla dessa smÂ detaljer skulle i stort leda till fˆrb‰ttring.

Fˆr att associera med det prototypen slutligen ska anv‰ndas till, n‰mligen fˆrb‰ttra fˆrbr‰nningen i en go-cart, skulle man ‰ven kunna t‰nka sig att m‰ta ytterligare en faktor n‰mligen m‰ngden luft som kommer in till fˆrbr‰nning genom fˆrgasaren. Det finns flera s‰tt att m‰ta detta, nÂgra mer noggranna ‰n andra. Ett enkelt s‰tt skulle vara att med hj‰lp av ett motstÂnd. MotstÂndet varierar sin resistans med temperaturen och kan med hj‰lp av det fÂ ett mÂtt pÂ hur snabbt go-carten f‰rdas. Om man vet hastigheten kan man r‰kna ut den m‰ngd luft som fÂngas upp av insuget till fˆrgasaren.
Om man sÂ vill skulle man kunna styra fˆrgasaren eller valfri komponent, fˆr att fˆrb‰ttra dess prestanda.

## 6 Referenser

http://www.engineersedge.com/basic_conversions.htm www.elfa.se
www.oru.se

Faktasˆkning :
AVR-programmering Kell MÂrdensjˆ, 2004.
Tips och idÈer om kretslˆsningar mm Torbjˆrn Andersson, 2004.
