grodansparadis/can4vscp_sanfrancisco_barometer/docs/barometer_files/baro-graph.gif

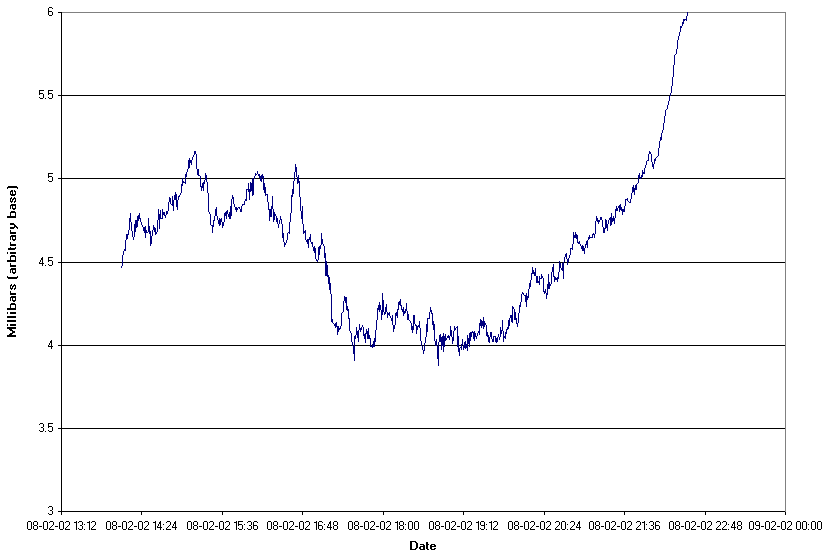
docs/barometer_files/baro-graph.gif
