grodansparadis/can4vscp_sanfrancisco_barometer/docs/barometer_files/baro-iv.jpg

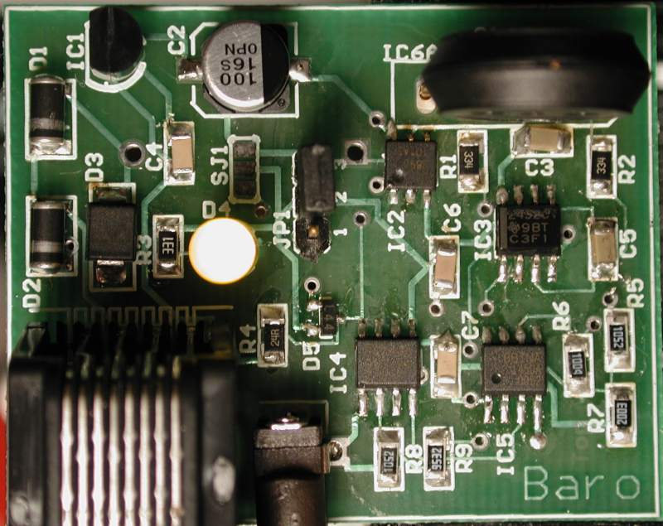
docs/barometer_files/baro-iv.jpg
