grodansparadis/can4vscp_sanfrancisco_barometer/docs/barometer_files/barobd1.jpg

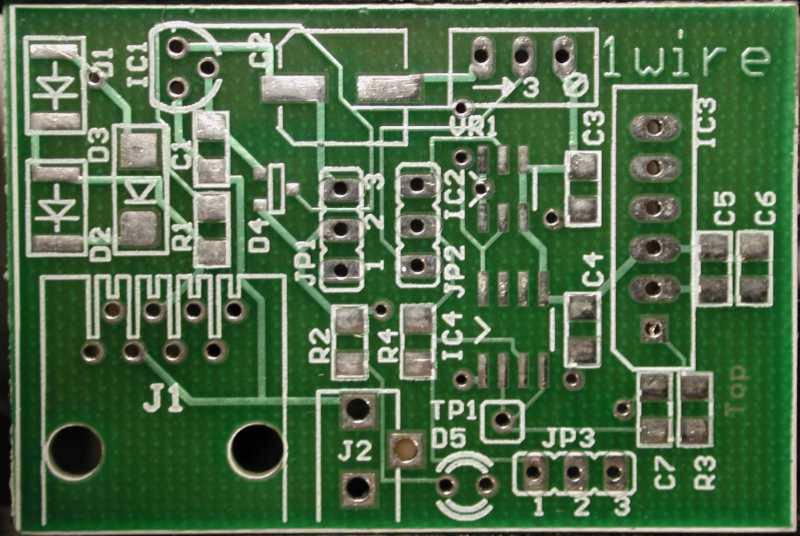
docs/barometer_files/barobd1.jpg
