grodansparadis/can4vscp_sanfrancisco_barometer/docs/barometer_files/barobd2.jpg

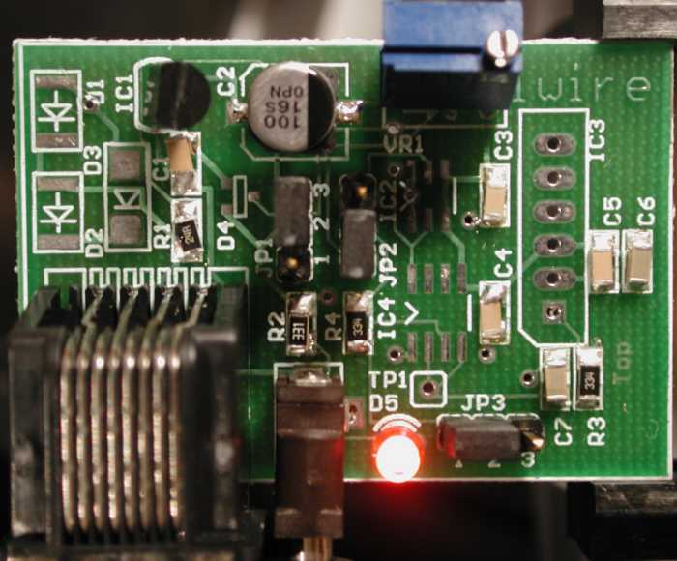
docs/barometer_files/barobd2.jpg
