grodansparadis/can4vscp_sanfrancisco_barometer/docs/BMP180 Barometric Pressure Sensor Hookup - learn.sparkfun.com_files/Readout.png

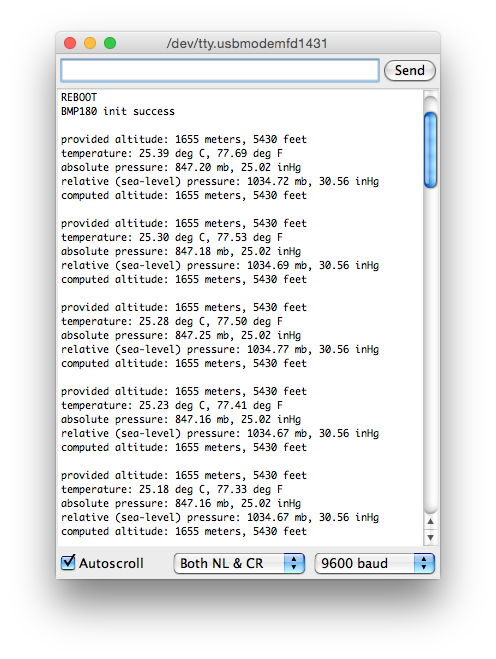
docs/BMP180 Barometric Pressure Sensor Hookup - learn.sparkfun.com_files/Readout.png
