grodansparadis/can4vscp_sanfrancisco_barometer/eagle/sanfranscisco_brd_rev_B.png

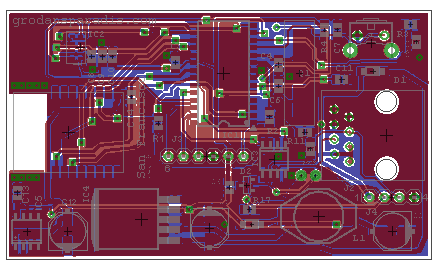
eagle/sanfranscisco_brd_rev_B.png
