grodansparadis/can4vscp_sanfrancisco_barometer/eagle/sanfranscisco_sch_rev_B.png

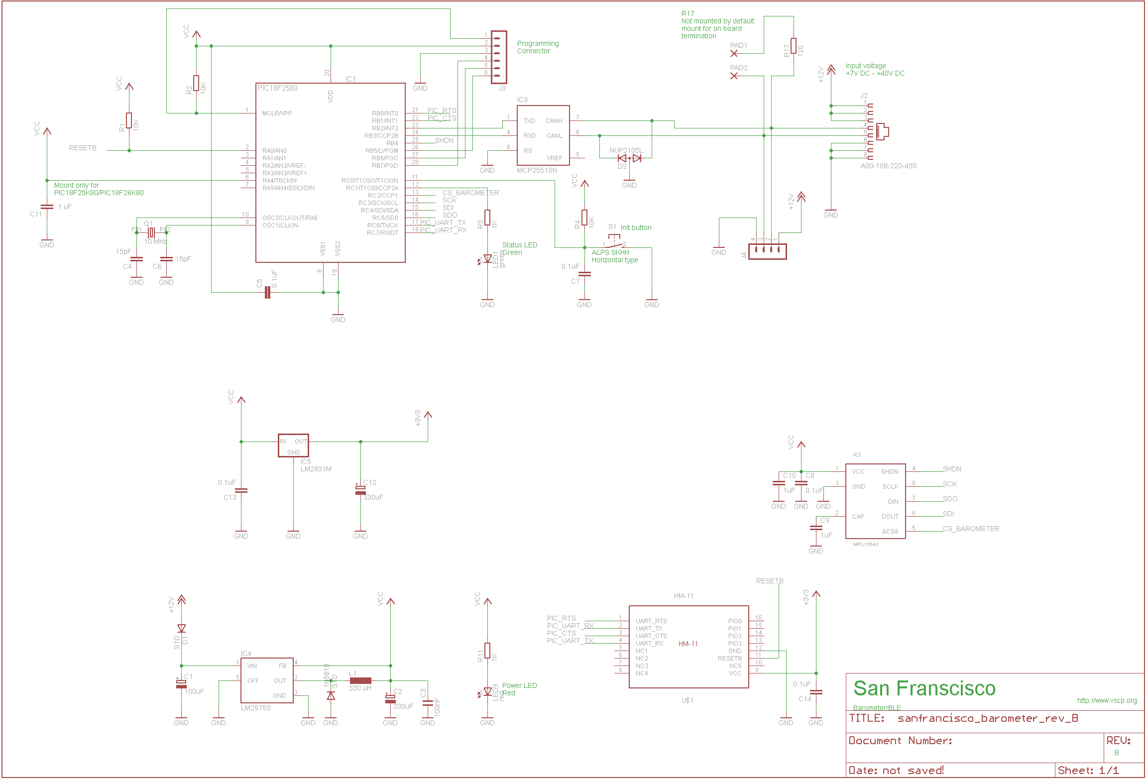
eagle/sanfranscisco_sch_rev_B.png
