grodansparadis/can4vscp_sanfrancisco_barometer/docs/pressure-v2.pdf

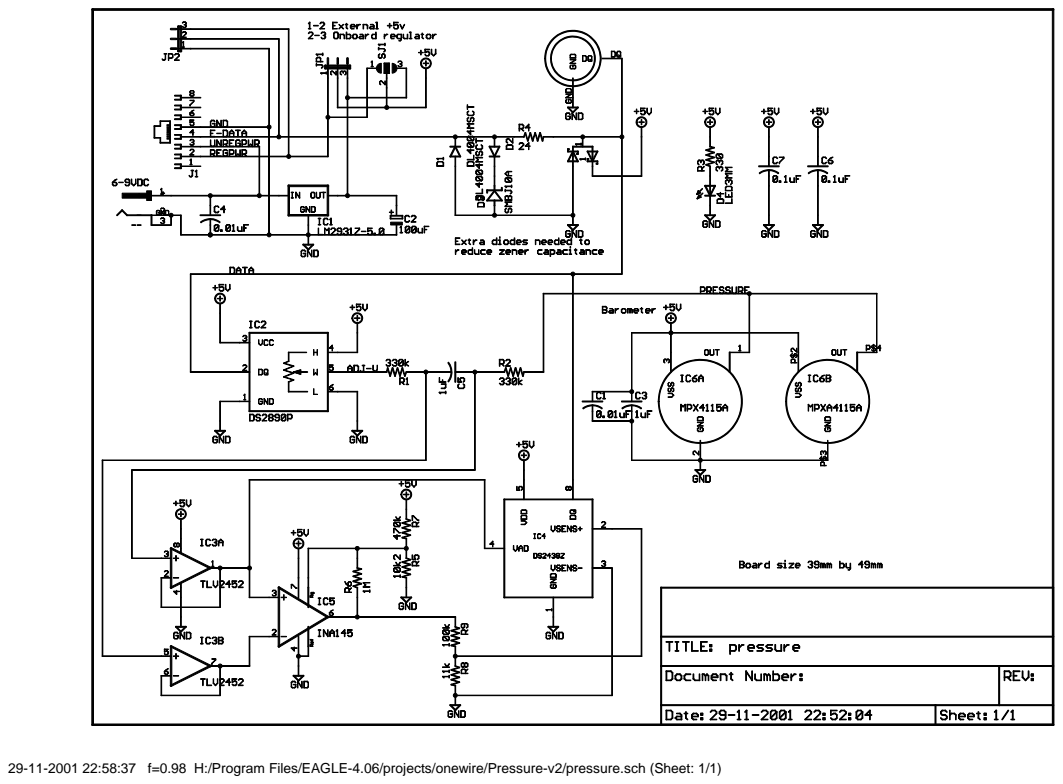
[picture p32: page 1]

29-11-2001 22:58:37 f=0.98 H:/Program Files/EAGLE-4.06/projects/onewire/Pressure-v2/pressure.sch (Sheet: 1/1)
